sinara-hw/Stabilizer/SIM/LT3042_DC2246A.asc

C1: cap; 10µ; Rser=1 Rpar=39K
C2: cap; 10µ; Rser=10m
C3: cap; 4.7µ; Rser=3m
C4: cap; 100n
C5: cap; 40µ; Rser=0.5
I1: current; PULSE(0 200u 0 10n 10n 500n 1u 100000)
I2: current; PULSE(0 200u 0 10n 10n 5000n 10u 100000)
I3: current; PULSE(0 200u 0 10n 10n 50u 100u 100000)
I4: current; PULSE(0 200u 0 10n 10n 500u 1000u 100000)
I5: current; PULSE(0 200u 0 10n 10n 5m 10m 100000)
R1: res; 200K
R2: res; 220
R3: res; 5k1
R4: res; 510
R5: res; 10
Rload: res; 220
U1: LT3042
U2: ADA4528-1
V1: voltage; 5
V2: voltage; 4.096
Named nets: 0, IN, OUT
.tran 0 3000m 10m startup
LT3042 - 20V, 200mA, Ultralow Noise, Ultrahigh PSRR RF Linear Regulator
Low Noise, High PSRR RF Linear Regulator
Input: 3.8V to 20V       Output: 3.3V @ 200mA
(Current limited internally by Vin to Vout differential, refer to datasheet)
